SHMakerspace/domenode/Hardware/Nodes/datasheets/esp32_pinout.jpg

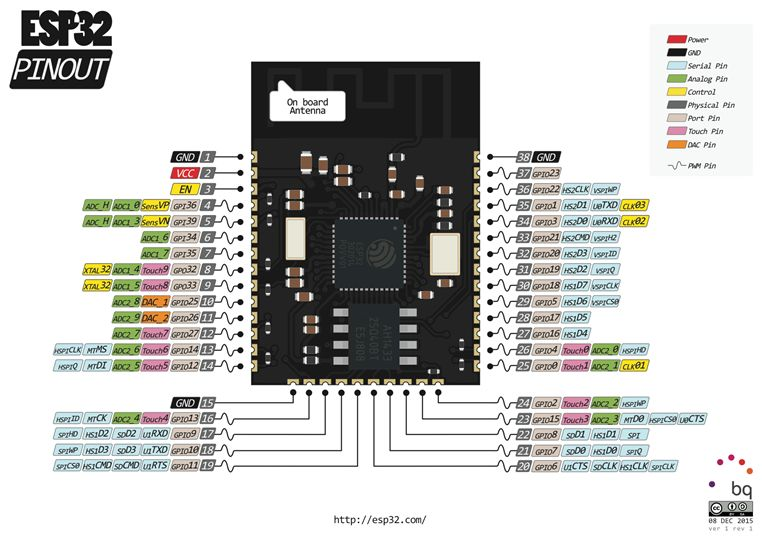
Hardware/Nodes/datasheets/esp32_pinout.jpg
