SHMakerspace/domenode/Hardware/Nodes/datasheets/mini-360_dimensions.jpg

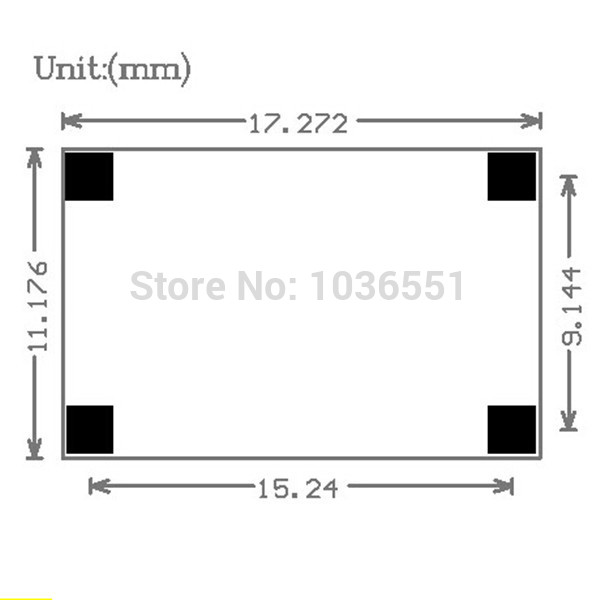
Hardware/Nodes/datasheets/mini-360_dimensions.jpg
